Artisfera/MP3-Gotchi/firmware/reversions/mp3gotchi-0.1.0/SpriteAssets.cpp

#include "SpriteAssets.h"

// HUD/monkey-bg1.png -> 96x64, non-black pixels: 2286
const AssetPixel ASSET_MONKEY_BG_PIXELS[] PROGMEM = {
  {42, 12, 0xFFFF},
  {43, 12, 0xFFFF},
  {44, 12, 0xFFFF},
  {45, 12, 0xFFFF},
  {46, 12, 0xFFFF},
  {47, 12, 0xFFFF},
  {48, 12, 0xFFFF},
  {49, 12, 0xFFFF},
  {50, 12, 0xFFFF},
  {51, 12, 0xFFFF},
  {52, 12, 0xFFFF},
  {53, 12, 0xFFFF},
  {38, 13, 0xFFFF},
  {39, 13, 0xFFFF},
  {40, 13, 0xFFFF},
  {41, 13, 0xFFFF},
  {42, 13, 0x7207},
  {43, 13, 0x7207},
  {44, 13, 0x7207},
  {45, 13, 0x7207},
  {46, 13, 0x7207},
  {47, 13, 0x7207},
  {48, 13, 0x7207},
  {49, 13, 0x7207},
  {50, 13, 0x7207},
  {51, 13, 0x7207},
  {52, 13, 0x7207},
  {53, 13, 0x7207},
  {54, 13, 0xFFFF},
  {55, 13, 0xFFFF},
  {56, 13, 0xFFFF},
  {57, 13, 0xFFFF},
  {36, 14, 0xFFFF},
  {37, 14, 0xFFFF},
  {38, 14, 0x7207},
  {39, 14, 0x7207},
  {40, 14, 0x7207},
  {41, 14, 0x7207},
  {42, 14, 0x7207},
  {43, 14, 0x7207},
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
};
extern const SparseAsset ASSET_MONKEY_BG = { 96, 64, 2286, ASSET_MONKEY_BG_PIXELS };

// Eyes/eyes-open1.png -> 96x64, non-black pixels: 132
const AssetPixel ASSET_EYES_OPEN_PIXELS[] PROGMEM = {
  {36, 24, 0x3145},
  {37, 24, 0x3145},
  {38, 24, 0x3145},
  {39, 24, 0x3145},
  {40, 24, 0x3145},
  {55, 24, 0x3145},
  {56, 24, 0x3145},
  {57, 24, 0x3145},
  {58, 24, 0x3145},
  {59, 24, 0x3145},
  {35, 25, 0x3145},
  {36, 25, 0x3145},
  {37, 25, 0x3145},
  {38, 25, 0x3145},
  {39, 25, 0xFFFF},
  {40, 25, 0x3145},
  {41, 25, 0x3145},
  {54, 25, 0x3145},
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
  {46, 59, 0xFFFF},
  {47, 59, 0xFFFF},
  {49, 59, 0xFFFF},
  {50, 59, 0xFFFF},
  {51, 59, 0xFFFF},
  {65, 59, 0xFFFF},
  {68, 59, 0xFFFF},
  {69, 59, 0xFFFF},
  {70, 59, 0xFFFF},
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
};
extern const SparseAsset ASSET_SONG_TITLE_AREA = { 96, 64, 162, ASSET_SONG_TITLE_AREA_PIXELS };
