Artisfera/MP3-Gotchi/firmware/reversions/mp3gotchi-0.1.10/AsepriteMiniFontData.h

#pragma once
#include <Arduino.h>

// Generated from the real Aseprite Mini font asset.
// Original font: Aseprite Font by David Capello.
// Original license: Creative Commons Attribution 4.0 International.
// Source license URL: https://github.com/aseprite/aseprite/blob/main/data/fonts/LICENSE.txt
// Modification: converted to compact C/C++ bitmap glyph data for MP3-Gotchi firmware.
// Source file: aseprite-mini.otf
constexpr uint8_t ASEPRITE_MINI_FONT_HEIGHT = 5;
constexpr uint8_t ASEPRITE_MINI_FONT_GLYPH_COUNT = 95;

struct AsepriteMiniGlyph {
  char code;
  uint8_t width;
  uint8_t rows[5];
};

const AsepriteMiniGlyph ASEPRITE_MINI_FONT[] PROGMEM = {
  {' ', 2, {0b00, 0b00, 0b00, 0b00, 0b00}},
  {'!', 2, {0b10, 0b10, 0b10, 0b00, 0b10}},
  {'"', 4, {0b1010, 0b1010, 0b0000, 0b0000, 0b0000}},
  {'#', 6, {0b010100, 0b111110, 0b010100, 0b111110, 0b010100}},
  {'$', 6, {0b011100, 0b101000, 0b011100, 0b001010, 0b011100}},
  {'%', 6, {0b110010, 0b110100, 0b001000, 0b010110, 0b100110}},
  {'&', 6, {0b010000, 0b101000, 0b010010, 0b101100, 0b010110}},
  {'\'', 2, {0b10, 0b10, 0b00, 0b00, 0b00}},
  {'(', 3, {0b010, 0b100, 0b100, 0b100, 0b010}},
  {')', 3, {0b100, 0b010, 0b010, 0b010, 0b100}},
  {'*', 4, {0b1010, 0b0100, 0b1110, 0b0100, 0b1010}},
  {'+', 4, {0b0000, 0b0100, 0b1110, 0b0100, 0b0000}},
  {',', 3, {0b000, 0b000, 0b000, 0b010, 0b100}},
  {'-', 3, {0b000, 0b000, 0b000, 0b110, 0b000}},
  {'.', 2, {0b00, 0b00, 0b00, 0b10, 0b00}},
  {'/', 4, {0b0010, 0b0010, 0b0100, 0b0100, 0b1000}},
  {'0', 4, {0b0100, 0b1010, 0b1010, 0b1010, 0b0100}},
  {'1', 3, {0b010, 0b110, 0b010, 0b010, 0b010}},
  {'2', 4, {0b1100, 0b0010, 0b0110, 0b1000, 0b1110}},
  {'3', 4, {0b1100, 0b0010, 0b0100, 0b0010, 0b1100}},
  {'4', 5, {0b00100, 0b01000, 0b10100, 0b11110, 0b00100}},
  {'5', 4, {0b1100, 0b1000, 0b1100, 0b0010, 0b1100}},
  {'6', 4, {0b0100, 0b1000, 0b1100, 0b1010, 0b0100}},
  {'7', 4, {0b1110, 0b0010, 0b0100, 0b0100, 0b0100}},
  {'8', 4, {0b0100, 0b1010, 0b0100, 0b1010, 0b0100}},
  {'9', 4, {0b0100, 0b1010, 0b0110, 0b0010, 0b0100}},
  {':', 2, {0b00, 0b10, 0b00, 0b10, 0b00}},
  {';', 3, {0b000, 0b010, 0b000, 0b000, 0b010}},
  {'<', 4, {0b0010, 0b0100, 0b1000, 0b0100, 0b0010}},
  {'=', 3, {0b000, 0b110, 0b000, 0b110, 0b000}},
  {'>', 4, {0b1000, 0b0100, 0b0010, 0b0100, 0b1000}},
  {'?', 5, {0b01100, 0b10010, 0b00100, 0b00000, 0b00100}},
  {'@', 5, {0b11110, 0b10110, 0b11010, 0b10110, 0b11110}},
  {'A', 4, {0b1110, 0b1010, 0b1010, 0b1110, 0b1010}},
  {'B', 4, {0b1110, 0b1010, 0b1100, 0b1010, 0b1110}},
  {'C', 4, {0b1110, 0b1000, 0b1000, 0b1000, 0b1110}},
  {'D', 4, {0b1100, 0b1010, 0b1010, 0b1010, 0b1100}},
  {'E', 4, {0b1110, 0b1000, 0b1110, 0b1000, 0b1110}},
  {'F', 4, {0b1110, 0b1000, 0b1110, 0b1000, 0b1000}},
  {'G', 4, {0b1110, 0b1000, 0b1000, 0b1010, 0b1110}},
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
};
